lab11/hail/3d/hail-debug/sam4l.SLDPRT

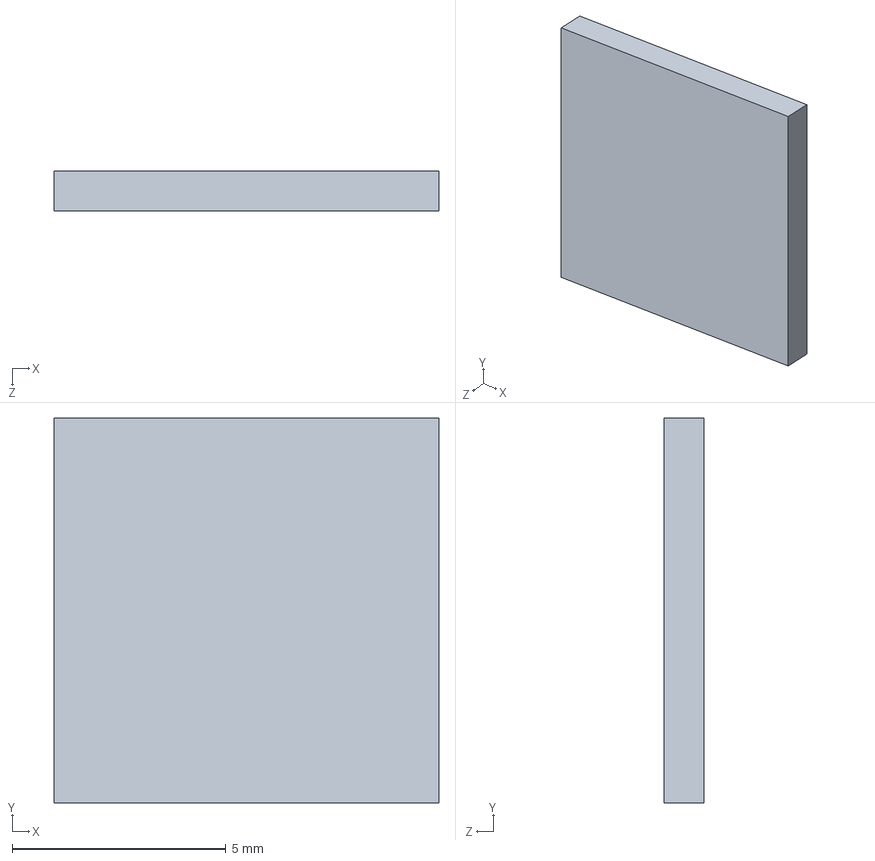
[picture p22: CAD file, 2017-03-14]
3d/hail-debug/sam4l.SLDPRT
9.00 x 9.00 x 0.94 mm
