lab11/hail/3d/mill-max-0985-0-15-20-71-14-11-0/mill-max-0985-0-15-20-71-14-11-0_9385-X.sldprt

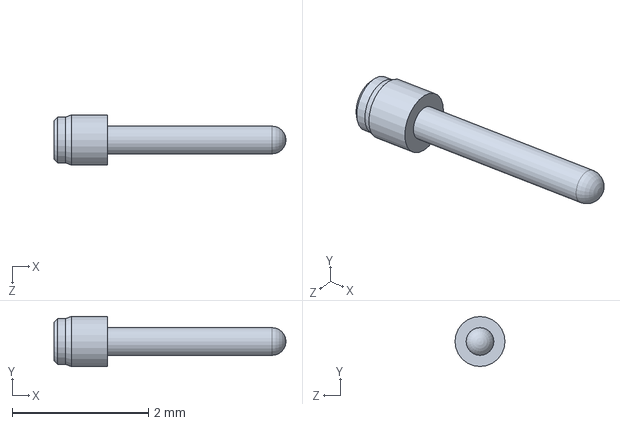
[picture p23: CAD file, 2017-03-14]
3d/mill-max-0985-0-15-20-71-14-11-0/mill-max-0985-0-15-20-71-14-11-0_9385-X.sldprt
3.40 x 0.734 x 0.734 mm
